LeKaZeD/ha-box/hardware/visuel/bc26e38f-751d-4385-8449-daee25fe1e48.PNG

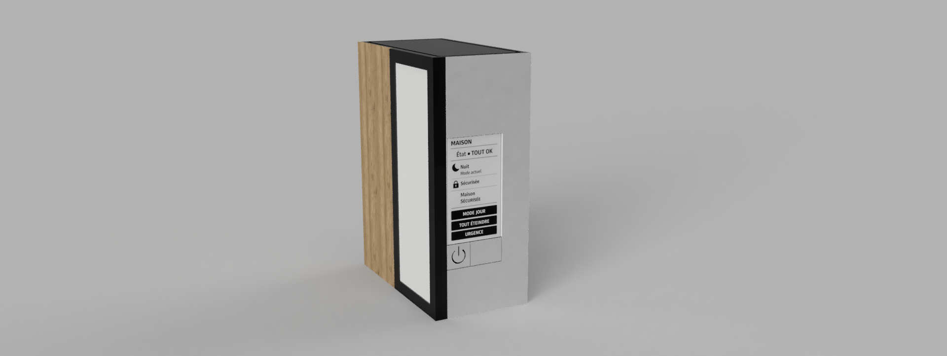
hardware/visuel/bc26e38f-751d-4385-8449-daee25fe1e48.PNG
