LeKaZeD/ha-box/hardware/visuel/ChatGPT Image 13 janv. 2026, 17_34_13_flipped.png

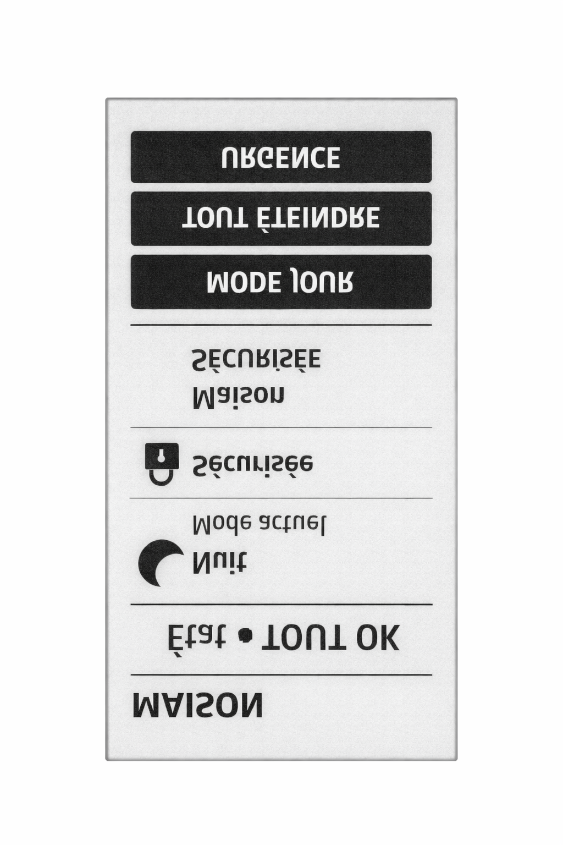
hardware/visuel/ChatGPT Image 13 janv. 2026, 17_34_13_flipped.png
