LeKaZeD/ha-box/hardware/visuel/Epaperscreen_flipped.png

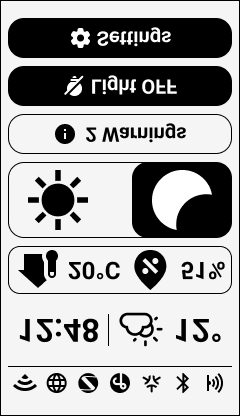
hardware/visuel/Epaperscreen_flipped.png
