LeKaZeD/ha-box/hardware/visuel/Home_assistant_box_2026-Jan-13_05-47-05PM-000_CustomizedView18560868933.png

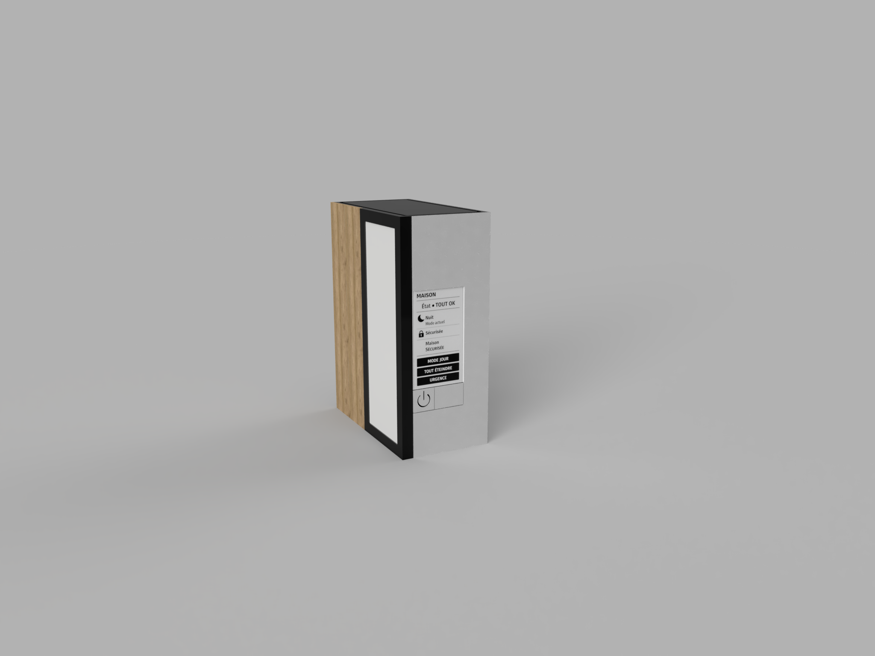
hardware/visuel/Home_assistant_box_2026-Jan-13_05-47-05PM-000_CustomizedView18560868933.png
