LeKaZeD/ha-box/hardware/visuel/Home_assistant_box_2026-Jan-13_05-50-02PM-000_CustomizedView49632287710.png

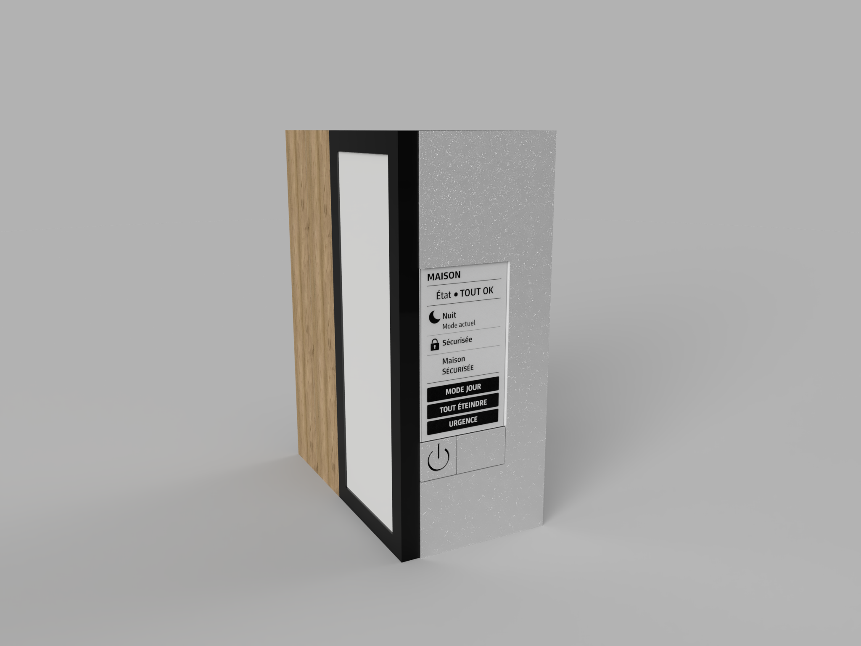
hardware/visuel/Home_assistant_box_2026-Jan-13_05-50-02PM-000_CustomizedView49632287710.png
