LeKaZeD/ha-box/hardware/visuel/Home_assistant_box_2026-Jan-13_05-50-42PM-000_CustomizedView2619306814.png

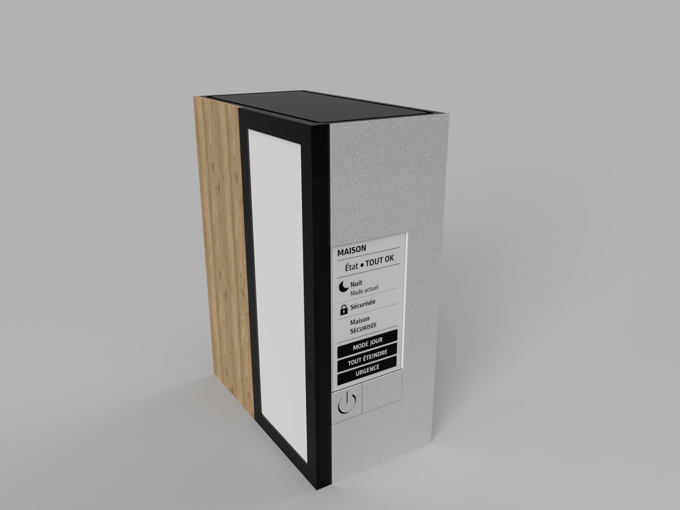
hardware/visuel/Home_assistant_box_2026-Jan-13_05-50-42PM-000_CustomizedView2619306814.png
