LeKaZeD/ha-box/hardware/visuel/Normal Screen.png

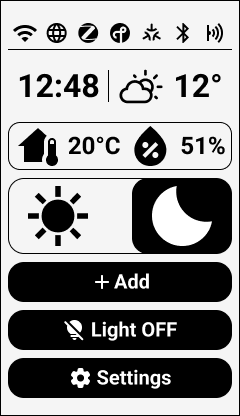
hardware/visuel/Normal Screen.png
