LeKaZeD/ha-box/ha-box-esp/src/settings_persistence.cpp

#include "settings_persistence.h"
#include "model/model.h"
#include <Arduino.h>
#include <Preferences.h>

static const char* SETTINGS_NAMESPACE = "habox";
static Preferences s_prefs;
static uint8_t s_lastBrightness = 255;
static bool s_lastSoundEnabled = true;
static uint8_t s_lastLanguage = 255;

void loadSettings(Model& model)
{
  if (!s_prefs.begin(SETTINGS_NAMESPACE, true)) {
    Serial2.println("[NVS] loadSettings: begin failed");
    return;
  }
  if (s_prefs.isKey("brightness")) {
    model.setBrightness(s_prefs.getUChar("brightness", 2));
  }
  if (s_prefs.isKey("sound")) {
    model.setSoundEnabled(s_prefs.getBool("sound", true));
  }
  if (s_prefs.isKey("lang")) {
    model.setLanguage(s_prefs.getUChar("lang", 0));
  }
  s_prefs.end();
  s_lastBrightness = model.settings.brightness;
  s_lastSoundEnabled = model.settings.sound_enabled;
  s_lastLanguage = model.settings.language;
}

void saveSettingsIfChanged(const Model& model)
{
  const bool changed = (model.settings.brightness != s_lastBrightness) ||
                       (model.settings.sound_enabled != s_lastSoundEnabled) ||
                       (model.settings.language != s_lastLanguage);
  if (!changed) return;
  s_lastBrightness = model.settings.brightness;
  s_lastSoundEnabled = model.settings.sound_enabled;
  s_lastLanguage = model.settings.language;
  if (!s_prefs.begin(SETTINGS_NAMESPACE, false)) {
    Serial2.println("[NVS] saveSettingsIfChanged: begin failed");
    return;
  }
  s_prefs.putUChar("brightness", s_lastBrightness);
  s_prefs.putBool("sound", s_lastSoundEnabled);
  s_prefs.putUChar("lang", s_lastLanguage);
  s_prefs.end();
}

// ---------------------------------------------------------------------------
// Fan configuration persistence
// Keys: fan_en (bool), fan_ton (float), fan_tfl (float)
// ---------------------------------------------------------------------------

bool loadFanConfig(FanPersistConfig& out)
{
  if (!s_prefs.begin(SETTINGS_NAMESPACE, true)) {
    Serial2.println("[NVS] loadFanConfig: begin failed");
    return false;
  }
  const bool exists = s_prefs.isKey("fan_en");
  if (exists) {
    out.enabled = s_prefs.getBool("fan_en",  false);
    out.tOn     = s_prefs.getFloat("fan_ton", 28.0f);
    out.tFull   = s_prefs.getFloat("fan_tfl", 60.0f);
  }
  s_prefs.end();
  if (!exists) return false;
  // Reject corrupted NVS data: tOn must be below tFull and within a sane range.
  if (out.tOn >= out.tFull || out.tOn < 0.0f || out.tFull > 100.0f) {
    Serial2.printf("[NVS] fan config invalid (tOn=%.1f tFull=%.1f), using defaults\n",
                   out.tOn, out.tFull);
    return false;
  }
  Serial2.printf("[NVS] fan loaded: en=%d tOn=%.1f tFull=%.1f\n",
                (int)out.enabled, out.tOn, out.tFull);
  return true;
}

void saveFanConfig(const FanPersistConfig& cfg)
{
  if (!s_prefs.begin(SETTINGS_NAMESPACE, false)) {
    Serial2.println("[NVS] saveFanConfig: begin failed");
    return;
  }
  s_prefs.putBool("fan_en",   cfg.enabled);
  s_prefs.putFloat("fan_ton", cfg.tOn);
  s_prefs.putFloat("fan_tfl", cfg.tFull);
  s_prefs.end();
  Serial2.printf("[NVS] fan saved: en=%d tOn=%.1f tFull=%.1f\n",
                (int)cfg.enabled, cfg.tOn, cfg.tFull);
}
