LeKaZeD/ha-box/ha-box/rootfs/usr/bin/ha-box/handlers/status_fetchers/matter.py

"""
Status fetcher: Matter (Matter integration in Core or Matter add-on).
Detects add-ons whose slug contains "matter", or Core entities with domain "matter".
"""

import logging
from typing import Dict, Any, Optional, List
from api.ha_api import HomeAssistantAPI

logger = logging.getLogger(__name__)


def _addon_slug_matches_matter(slug: str) -> bool:
    """True if this add-on slug indicates Matter."""
    if not slug:
        return False
    return "matter" in slug.lower()


def fetch_matter(ha_api: HomeAssistantAPI, addons_list: Optional[List[Dict[str, Any]]] = None) -> Dict[str, Any]:
    """
    Detect Matter: add-on running or Matter integration loaded in Core.

    Args:
        ha_api: API client.
        addons_list: Optional pre-fetched add-ons list (avoids duplicate GET /addons).

    Returns:
        Dict with key: matter_ok (bool).
    """
    out: Dict[str, Any] = {"matter_ok": False}
    try:
        # 1) Add-ons: any Matter add-on started
        if addons_list is None:
            addons_list = ha_api.get_addons_list()
        if isinstance(addons_list, list):
            for addon in addons_list:
                if not isinstance(addon, dict):
                    continue
                slug = addon.get("slug", "")
                state = addon.get("state", "")
                if _addon_slug_matches_matter(slug) and state in ("started", "running"):
                    out["matter_ok"] = True
                    return out
        # 2) Core config entries: Matter integration (domain="matter"), loaded and not disabled
        entries = ha_api.get_config_entries()
        if isinstance(entries, list):
            for entry in entries:
                if not isinstance(entry, dict):
                    continue
                if entry.get("disabled_by"):
                    continue
                if entry.get("domain") == "matter" and entry.get("state") == "loaded":
                    out["matter_ok"] = True
                    return out
    except Exception as e:
        logger.debug("fetch_matter failed: %s", e)
    return out
