LeKaZeD/ha-box/ha-box-esp/src/ui/widgets/widget_temp.h

#pragma once
#include "widget_base.h"
#include "../../model/model.h"
#include "../assets/icons_draw.h"
#include "../assets/icons_min.h"

struct TempWidget : public WidgetBase<TempWidget>
{
  enum class Kind : uint8_t { Indoor, Outdoor };
  Kind kind;

  // UI config
  const GFXfont* font = nullptr;  // ex: &MyFont18pt7b
  bool showLabel = true;
  const char* label = nullptr;    // "IN" / "OUT"

  explicit TempWidget(Rect rr, Kind k) : WidgetBase<TempWidget>(rr), kind(k) {}

  void applyDirty(uint32_t dirtyMask)
  {
    if (kind == Kind::Indoor)  { if (dirtyMask & (DK_HM_TempIn | DK_HM_Humidity)) dirty = true; }
    if (kind == Kind::Outdoor) { if (dirtyMask & DK_HM_TempOut) dirty = true; }
  }

  template<typename DisplayT>
  void draw(DisplayT& display, const Model& model)
  {
    display.setTextColor(GxEPD_BLACK);
    
    if (kind == Kind::Indoor)
    {
      // Indoor temp (home_temp_48x48 icon) + humidity (humidity_48x48 icon), side by side
      static uint8_t tmp[384]; // 48x48: 6 bytes/row × 48 rows = 288 bytes

      // 1) Indoor temperature icon (48x48)
      const int16_t tempIconX = r.x + 2;
      const int16_t tempIconY = r.y + 2;
      drawIcon_0Black(display, tempIconX, tempIconY, home_temp_48x48, 48, 48, GxEPD_BLACK, GxEPD_WHITE, tmp);
      
      // 2) Rounded temperature (no decimals) - right of icon
      const int16_t t = model.home.temp_in_x10;
      const int16_t rounded = (t >= 0) ? (t + 5) / 10 : (t - 5) / 10;
      
      char tempBuf[6]; // "-99" max = 4 chars + '\0'
      snprintf(tempBuf, sizeof(tempBuf), "%d", rounded);
      
      const int16_t tempX = r.x + 50; // After 48x48 icon + margin
      const int16_t tempY = r.y + 35; // Vertically centered with icon
      
      display.setFont(font);
      display.setCursor(tempX, tempY);
      display.print(tempBuf);
      
      int16_t x1, y1;
      uint16_t w, h;
      display.getTextBounds(tempBuf, tempX, tempY, &x1, &y1, &w, &h);

      // Degree symbol
      const int16_t degCx = tempX + w + 7;
      const int16_t degCy = tempY - h + 6;
      drawDegreeSymbol(display, degCx, degCy, 5);
      
      // "C"
      display.setCursor(tempX + w + 12, tempY);
      display.print("C");
      
      // 3) Humidity icon (48x48) - below temp
      const int16_t humIconX = r.x + 115;
      const int16_t humIconY = r.y + 2; // After temp icon (2 + 48 + 2 = 52)
      drawIcon_0Black(display, humIconX, humIconY, humidity_48x48, 48, 48, GxEPD_BLACK, GxEPD_WHITE, tmp);
      
      // 4) Humidity value - right of icon
      char humBuf[6]; // "99%" max = 4 chars + '\0'
      snprintf(humBuf, sizeof(humBuf), "%u%%", model.home.humidity);
      
      const int16_t humX = r.x + 160; // Same alignment as temperature
      const int16_t humY = r.y + 35;  // Vertically centered with humidity icon
      
      display.setFont(font);
      display.setCursor(humX, humY);
      display.print(humBuf);
    }
    else
    {
      // Outdoor: original behaviour (no icon for now)
      const int16_t t = model.home.temp_out_x10;
      const int16_t rounded = (t >= 0) ? (t + 5) / 10 : (t - 5) / 10;
      
      char buf[6];
      snprintf(buf, sizeof(buf), "%d", rounded);
      
      display.setFont(font);
      const int16_t baseX = r.x + 2;
      const int16_t baseY = r.y + r.h - 6;
      
      display.setCursor(baseX, baseY);
      display.print(buf);
      
      int16_t x1, y1;
      uint16_t w, h;
      display.getTextBounds(buf, baseX, baseY, &x1, &y1, &w, &h);
      
      const int16_t degCx = baseX + w + 6;
      const int16_t degCy = baseY - h + 6;
      drawDegreeSymbol(display, degCx, degCy, 5);
      
      display.setCursor(baseX + w + 10, baseY);
      display.print("C");
    }
    
    display.drawRoundRect(r.x, r.y, r.w, r.h, 16, GxEPD_BLACK);
  }
};
