LeKaZeD/ha-box/ha-box-esp/src/ui/page_shutdown.h

#pragma once
#include "page.h"
#include "../i18n.h"
#include "assets/icons_draw.h"

template<typename DisplayT>
struct PageShutdown : public Page<DisplayT>
{
  static constexpr int16_t ICON_SIZE  = 72;
  static constexpr int16_t BOX_PAD    = 16;
  static constexpr int16_t BOX_RADIUS = 16;
  static constexpr int16_t BOX_SIZE   = ICON_SIZE + BOX_PAD * 2;

  const GFXfont* fontTitle    = nullptr;
  const GFXfont* fontSubtitle = nullptr;
  const GFXfont* fontHint     = nullptr;
  const uint8_t* icon         = nullptr;

  void setFonts(const GFXfont* title, const GFXfont* subtitle, const GFXfont* hint)
  {
    fontTitle    = title;
    fontSubtitle = subtitle;
    fontHint     = hint;
  }

  void setIcon(const uint8_t* bmp) { icon = bmp; }

  void drawFull(DisplayT& display, const Model&) override
  {
    display.setFullWindow();
    display.firstPage();
    do {
      display.fillScreen(GxEPD_WHITE);
      drawContent(display);
    } while (display.nextPage());
  }

  void applyDirty(uint32_t) override {}
  void renderPartials(DisplayT&, const Model&, uint8_t) override {}
  void tick(Model&) override {}

private:
  void drawContent(DisplayT& display)
  {
    const LangShutdown& L = i18n::shutdown();
    display.setTextColor(GxEPD_BLACK);

    int16_t cursorY = 0;

    // Title
    if (fontTitle) {
      display.setFont(fontTitle);
      int16_t x1, y1;
      uint16_t tw, th;
      display.getTextBounds(L.title, 0, 0, &x1, &y1, &tw, &th);
      cursorY = 24;
      display.setCursor((DISPLAY_W - (int16_t)tw) / 2, cursorY - y1);
      display.print(L.title);
      cursorY += (int16_t)th + 8;
    }

    cursorY += 8;

    // Subtitle lines (centered, below title)
    if (fontSubtitle) {
      display.setFont(fontSubtitle);
      int16_t x1, y1;
      uint16_t tw, th;

      display.getTextBounds(L.subtitleLine1, 0, 0, &x1, &y1, &tw, &th);
      display.setCursor((DISPLAY_W - (int16_t)tw) / 2, cursorY - y1);
      display.print(L.subtitleLine1);
      cursorY += (int16_t)th + 6;

      display.getTextBounds(L.subtitleLine2, 0, 0, &x1, &y1, &tw, &th);
      display.setCursor((DISPLAY_W - (int16_t)tw) / 2, cursorY - y1);
      display.print(L.subtitleLine2);
    }

    // Power icon centered in the middle of the screen, inside a rounded box
    if (icon) {
      const int16_t boxX  = (DISPLAY_W - BOX_SIZE) / 2;
      const int16_t boxY  = DISPLAY_H / 2 - BOX_SIZE / 2;
      const int16_t iconX = boxX + BOX_PAD;
      const int16_t iconY = boxY + BOX_PAD;
      display.drawRoundRect(boxX, boxY, BOX_SIZE, BOX_SIZE, BOX_RADIUS, GxEPD_BLACK);
      display.fillRect(iconX, iconY, ICON_SIZE, ICON_SIZE, GxEPD_WHITE);
      static uint8_t iconBuf[648];
      drawIcon_0Black(display, iconX, iconY, icon, ICON_SIZE, ICON_SIZE,
                      GxEPD_BLACK, GxEPD_WHITE, iconBuf);
    }

    // Hint lines at the bottom
    if (fontHint) {
      display.setFont(fontHint);
      int16_t x1, y1;
      uint16_t tw, th;

      display.getTextBounds(L.hintLine1, 0, 0, &x1, &y1, &tw, &th);
      const int16_t lineH  = (int16_t)th + 4;
      const int16_t hint2Y = DISPLAY_H - MARGIN - (int16_t)th;
      const int16_t hint1Y = hint2Y - lineH;

      display.setCursor((DISPLAY_W - (int16_t)tw) / 2, hint1Y - y1);
      display.print(L.hintLine1);

      display.getTextBounds(L.hintLine2, 0, 0, &x1, &y1, &tw, &th);
      display.setCursor((DISPLAY_W - (int16_t)tw) / 2, hint2Y - y1);
      display.print(L.hintLine2);
    }
  }
};
