LeKaZeD/ha-box/ha-box-esp/src/ui/widgets/rect.h

#pragma once
#include <stdint.h>

struct Rect
{
  int16_t x = 0;
  int16_t y = 0;
  int16_t w = 0;
  int16_t h = 0;

  bool contains(int16_t px, int16_t py) const
  {
    return px >= x && px < x + w && py >= y && py < y + h;
  }
};
